cwill713/Solar-Panel-Phone-Charger/Simulations/Pictures of Output Voltage/0.05s.PNG

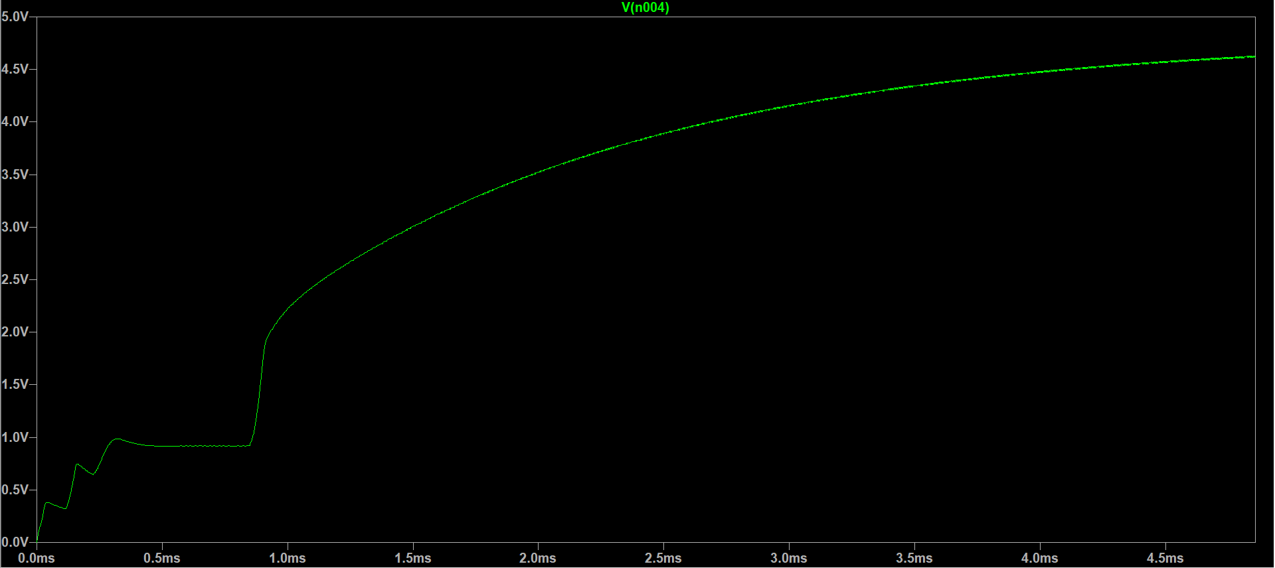
Simulations/Pictures of Output Voltage/0.05s.PNG
