cwill713/Solar-Panel-Phone-Charger/Simulations/Pictures of Output Voltage/Capture.PNG

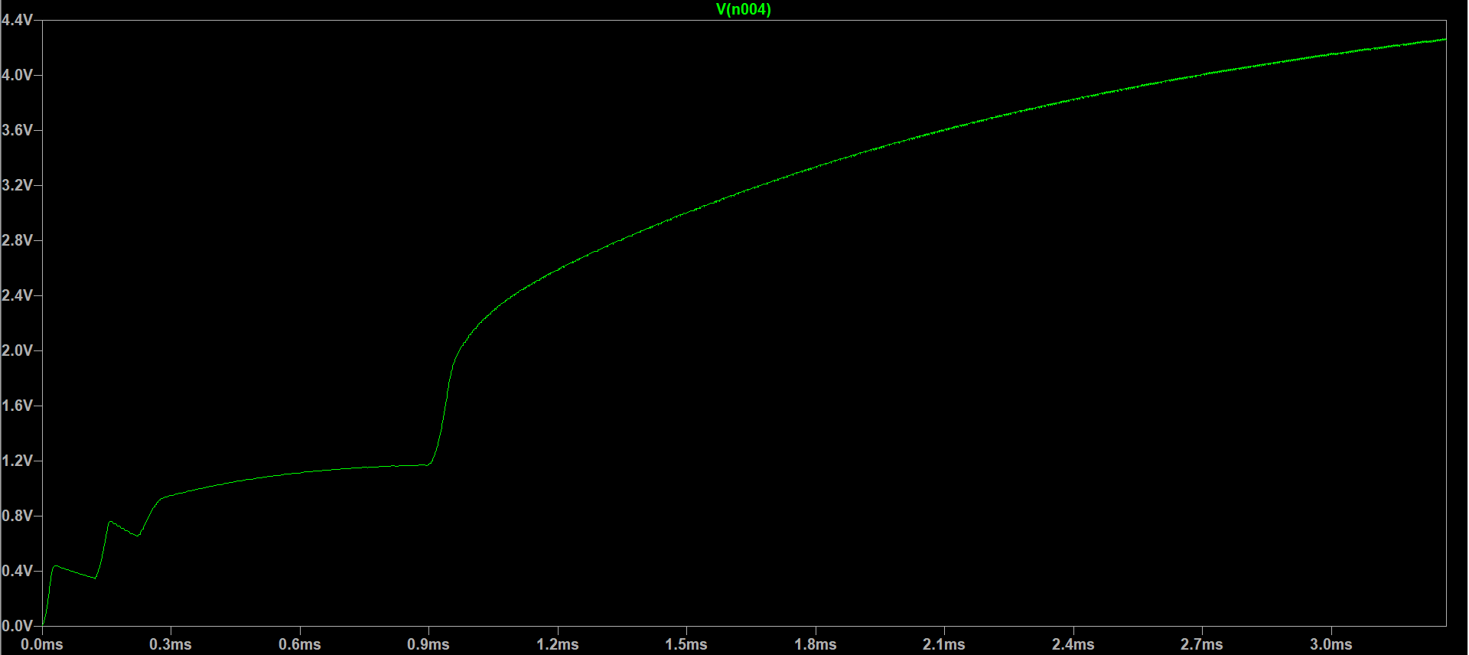
Simulations/Pictures of Output Voltage/Capture.PNG
