cwill713/Solar-Panel-Phone-Charger/Simulations/Pictures of Output Voltage/ThreeOutputVoltages.PNG

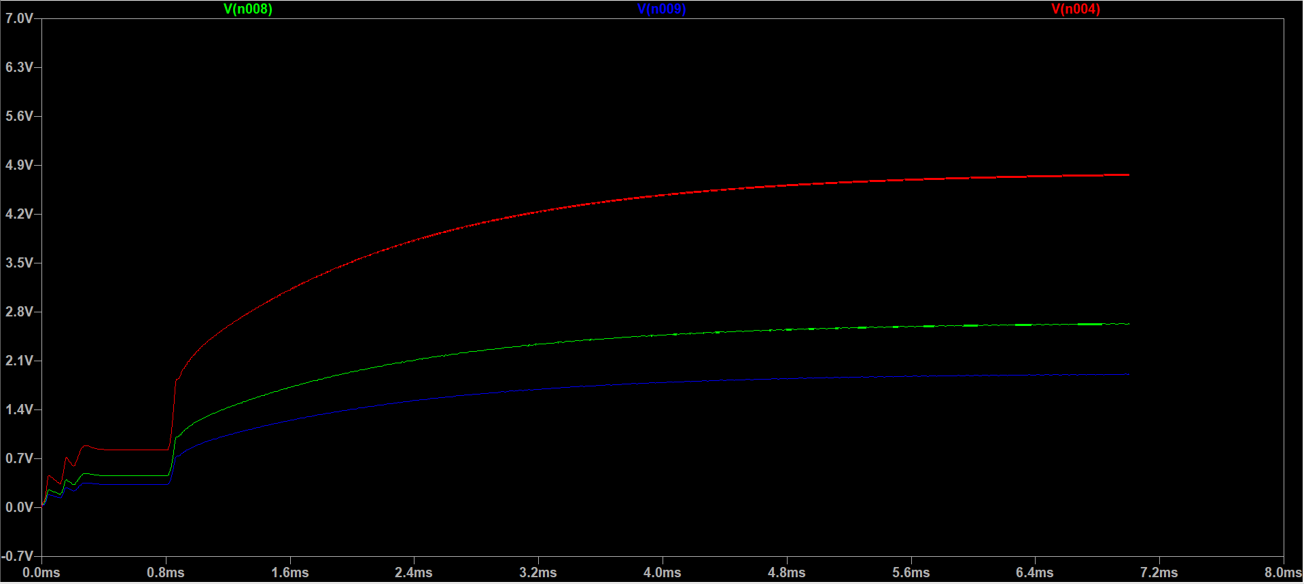
Simulations/Pictures of Output Voltage/ThreeOutputVoltages.PNG
