cwill713/Solar-Panel-Phone-Charger/Schematics/SolarChargerV3/PDF Files/SolarChargerV2-B_Silkscreen.pdf

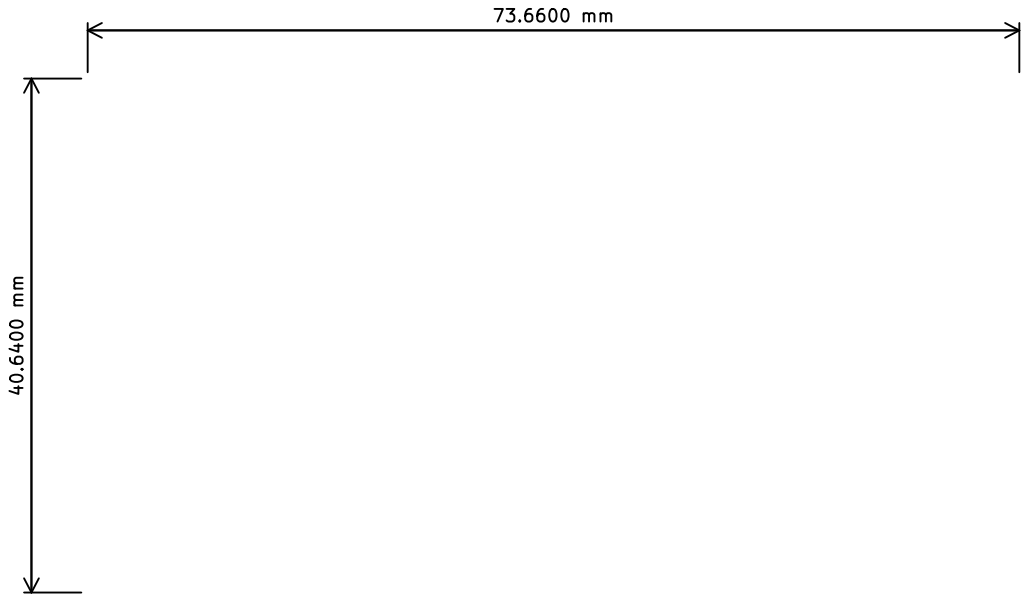
[picture p18: page 1]
