cwill713/Solar-Panel-Phone-Charger/Schematics/SolarChargerV3/PDF Files/SolarChargerV2-F_Cu.pdf

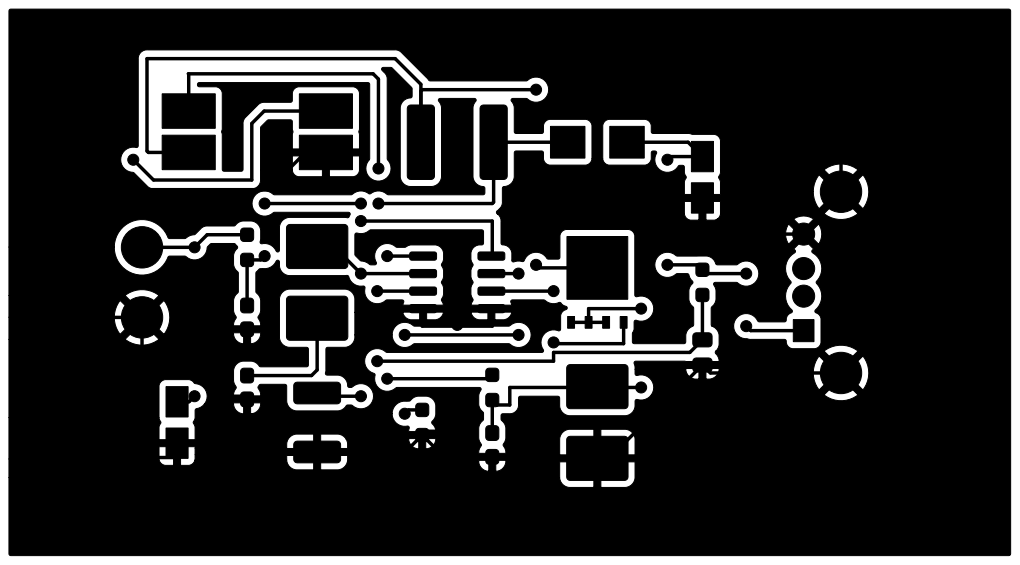
[picture p19: page 1]
