cwill713/Solar-Panel-Phone-Charger/Schematics/SolarChargerV3/PDF Files/SolarChargerV2-F_Fab.pdf

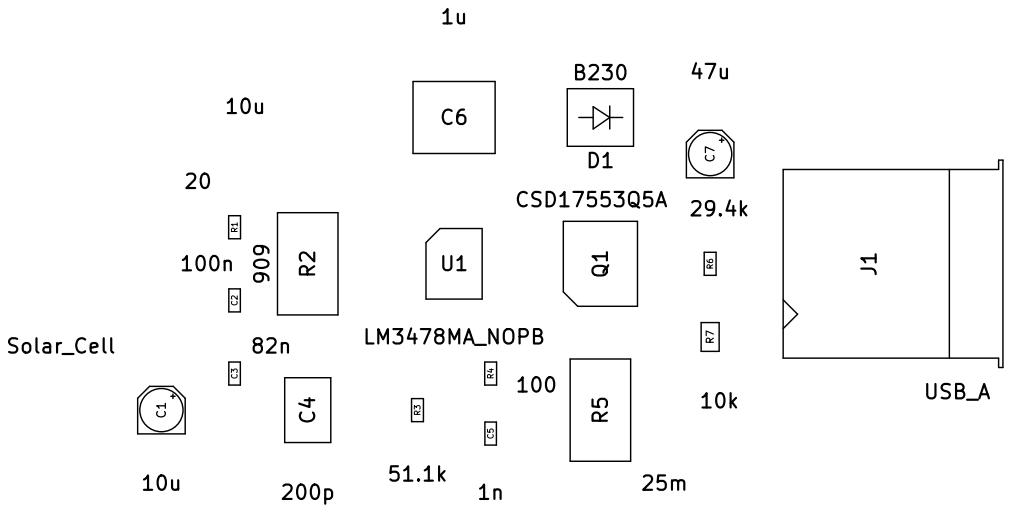
[picture p20: page 1]
