cwill713/Solar-Panel-Phone-Charger/Schematics/SolarChargerV3/PDF Files/SolarChargerV2-F_Mask.pdf

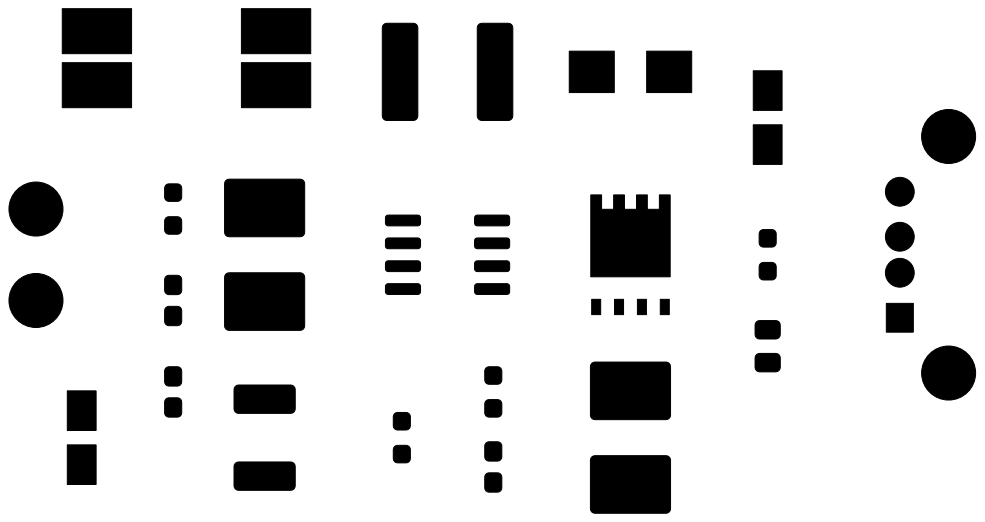
[picture p21: page 1]
