cwill713/Solar-Panel-Phone-Charger/Schematics/SolarChargerV3/PDF Files/SolarChargerV2-F_Silkscreen.pdf

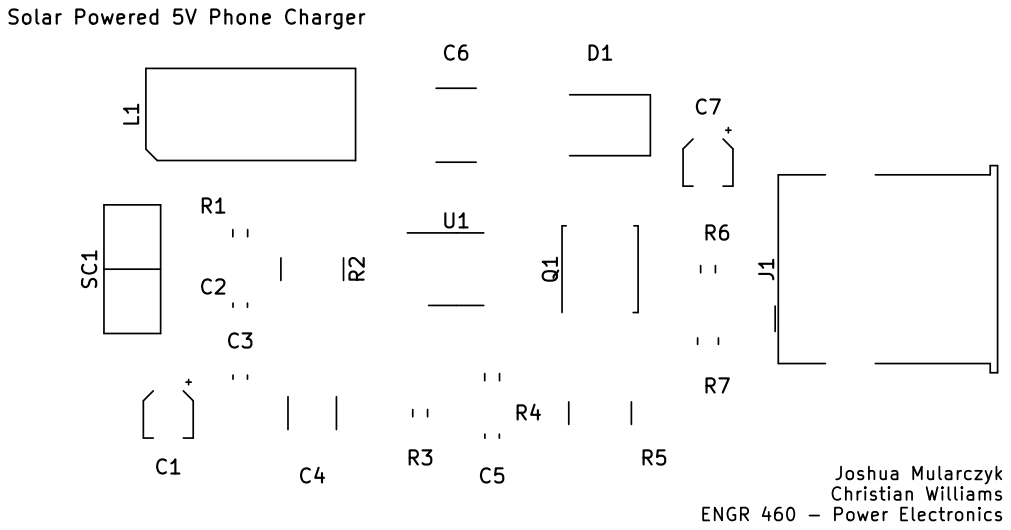
[picture p22: page 1]
