cwill713/Solar-Panel-Phone-Charger/Schematics/SolarChargerV4/PDF Files/SolarChargerV2-F_Cu.pdf

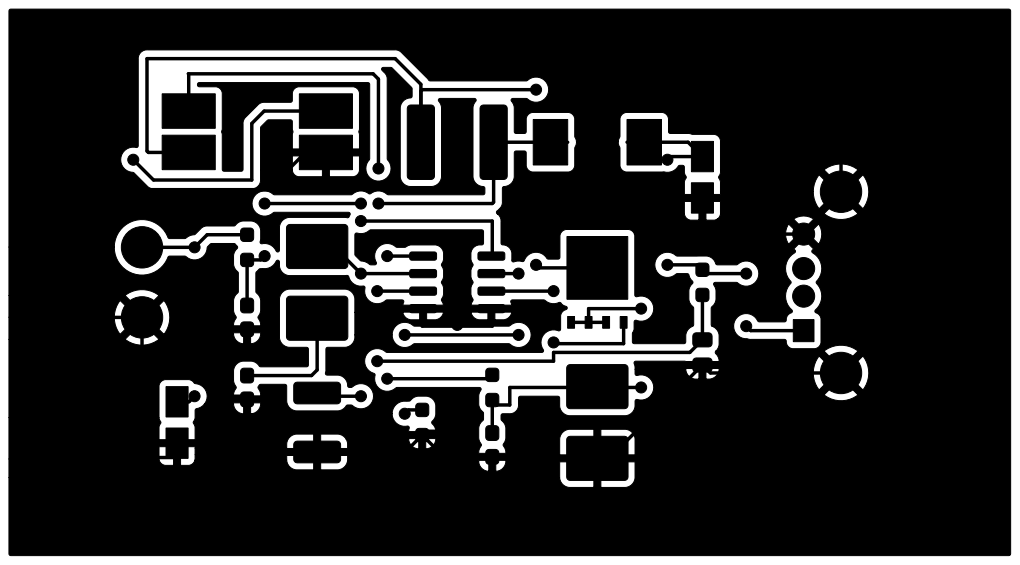
[picture p23: page 1]
