cwill713/Solar-Panel-Phone-Charger/Schematics/SolarChargerV4/PDF Files/SolarChargerV2-F_Fab.pdf

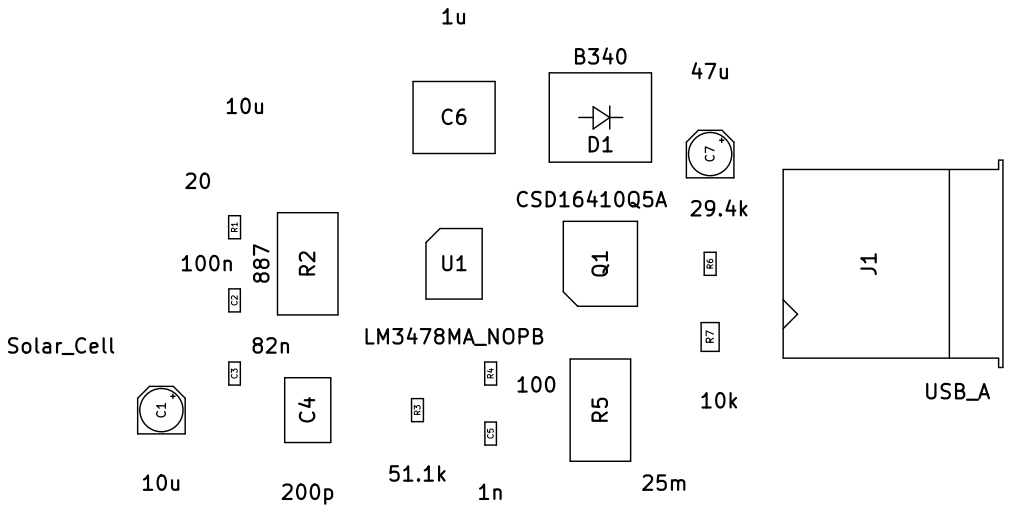
[picture p24: page 1]
