cwill713/Solar-Panel-Phone-Charger/Schematics/SolarChargerV4/PDF Files/SolarChargerV2-F_Mask.pdf

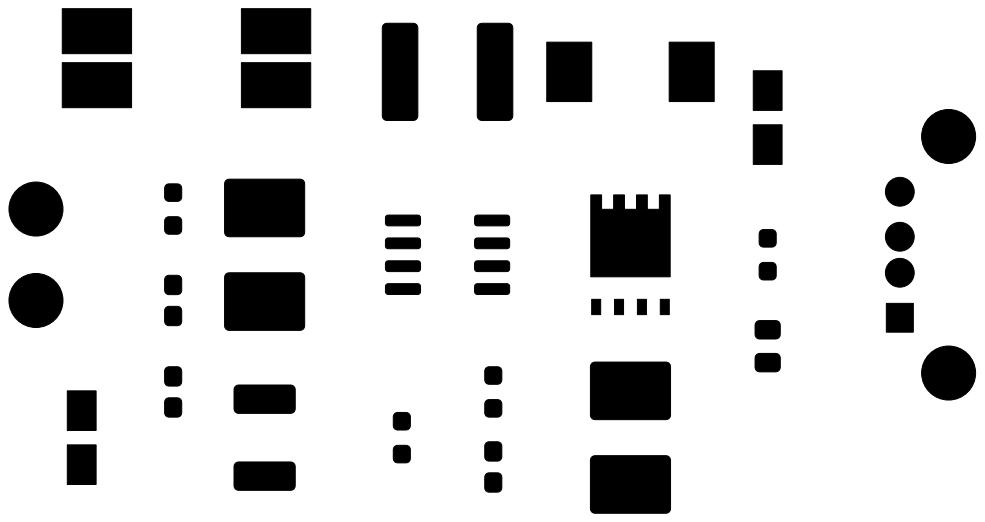
[picture p25: page 1]
