cwill713/Solar-Panel-Phone-Charger/Schematics/SolarChargerV4/PDF Files/SolarChargerV2-F_Silkscreen.pdf

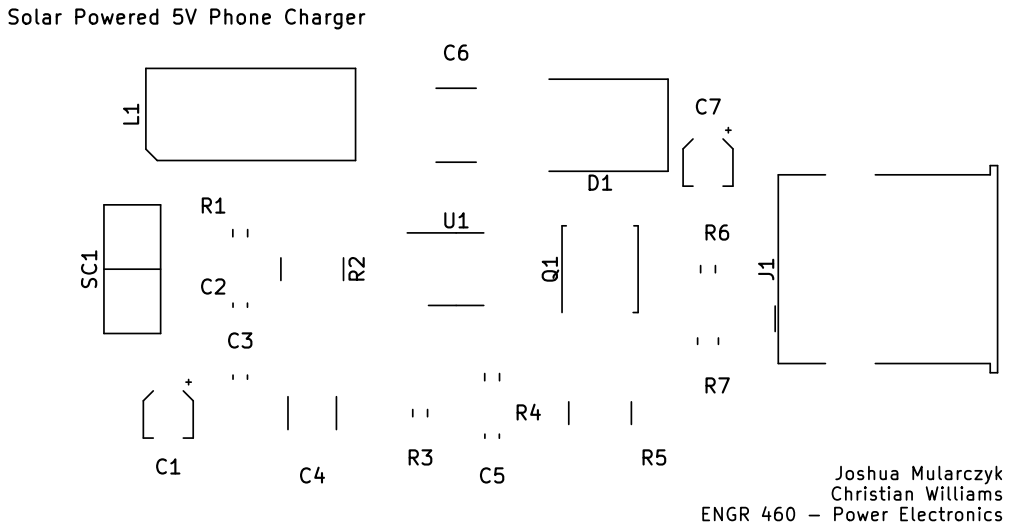
[picture p26: page 1]
