cwill713/Solar-Panel-Phone-Charger/Schematics/SolarChargerV5/PDFV5Files/SolarChargerV2-B_Cu.pdf

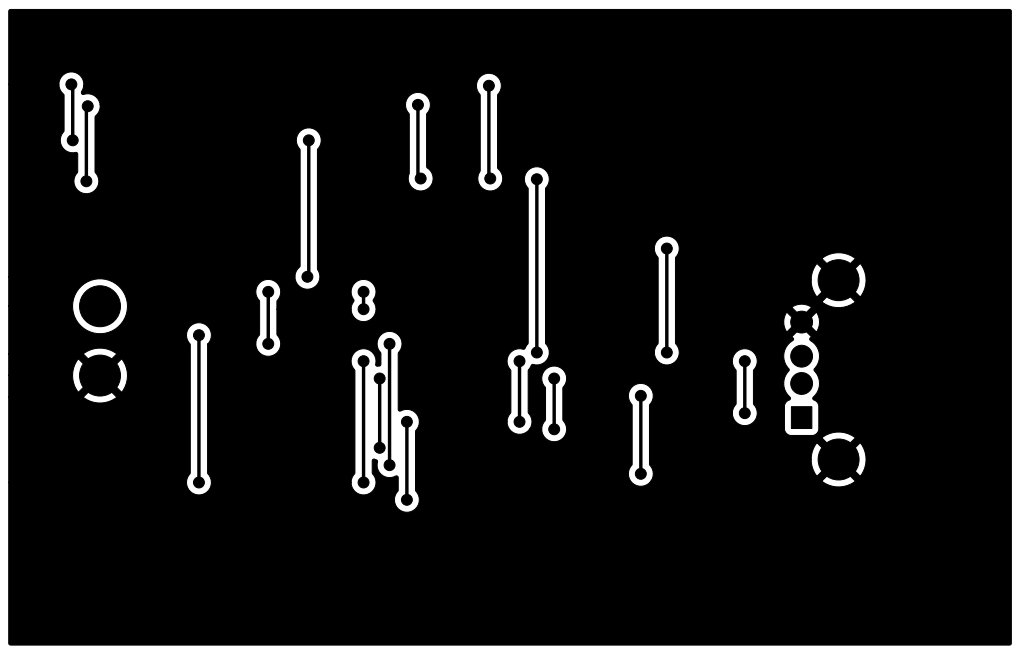
[picture p27: page 1]
