cwill713/Solar-Panel-Phone-Charger/Schematics/SolarChargerV5/PDFV5Files/SolarChargerV2-B_Mask.pdf

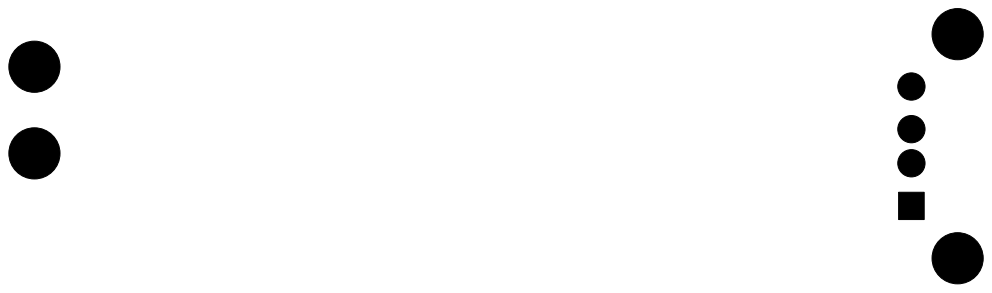
[picture p28: page 1]
