cwill713/Solar-Panel-Phone-Charger/Schematics/SolarChargerV5/PDFV5Files/SolarChargerV2-F_Cu.pdf

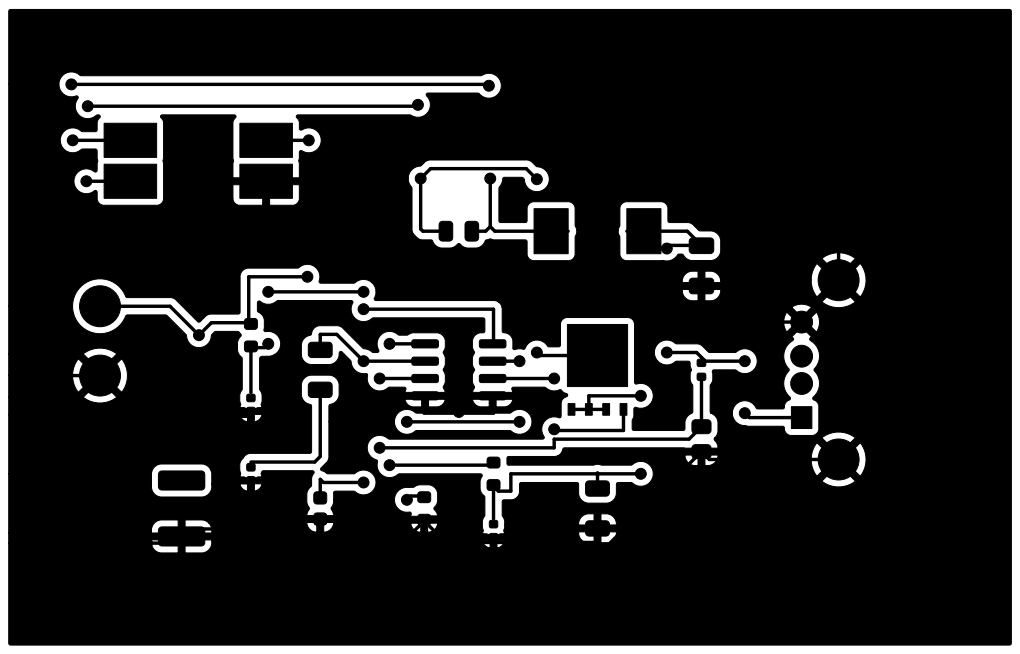
[picture p29: page 1]
