cwill713/Solar-Panel-Phone-Charger/Schematics/SolarChargerV5/PDFV5Files/SolarChargerV2-F_Fab.pdf

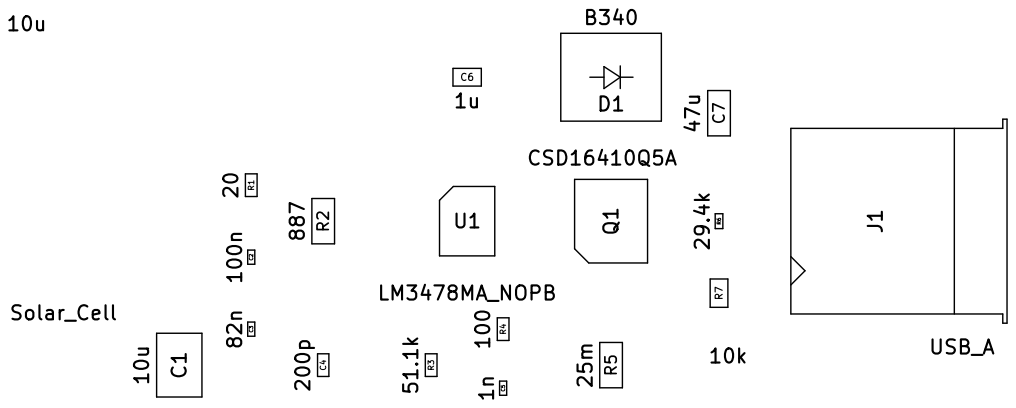
[picture p30: page 1]
