cwill713/Solar-Panel-Phone-Charger/Schematics/SolarChargerV5/PDFV5Files/SolarChargerV2-F_Mask.pdf

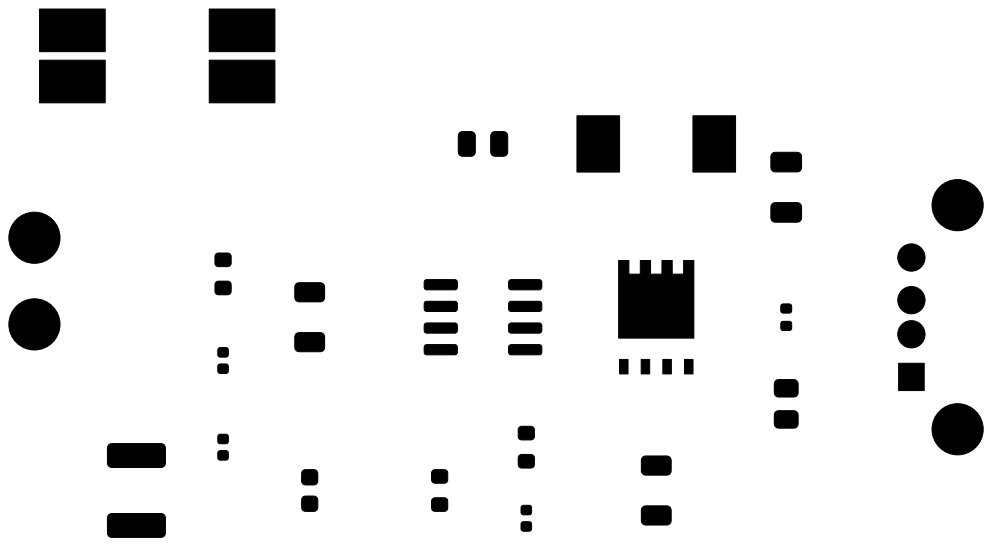
[picture p31: page 1]
