cwill713/Solar-Panel-Phone-Charger/Schematics/SolarChargerV5/PDFV5Files/SolarChargerV2-F_Silkscreen.pdf

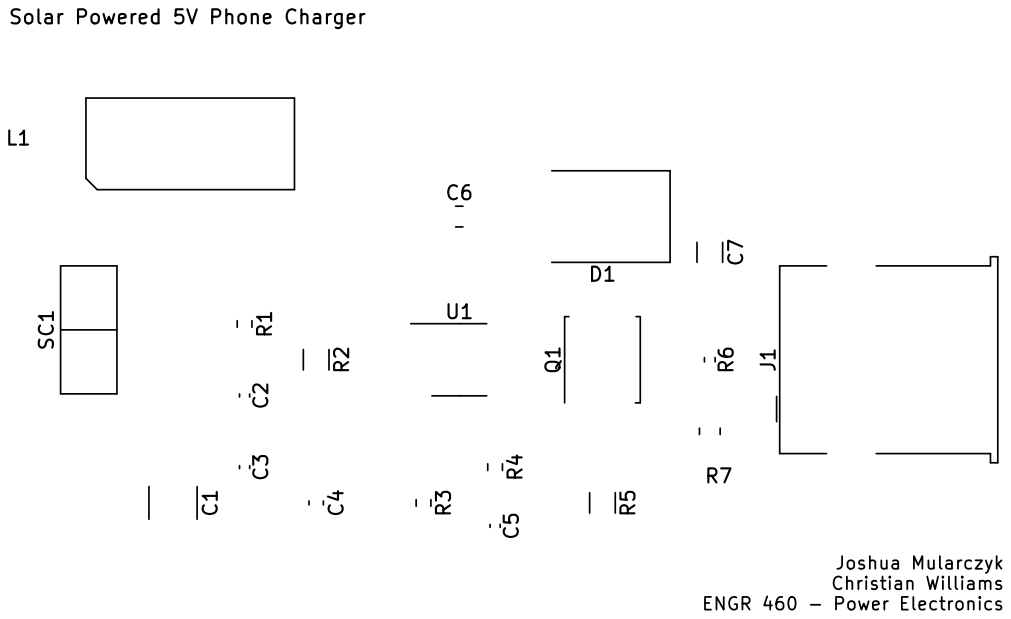
[picture p32: page 1]
