cwill713/Solar-Panel-Phone-Charger/Schematics/SolarChargerV6/PDFV6Files/SolarChargerV6-B_Cu.pdf

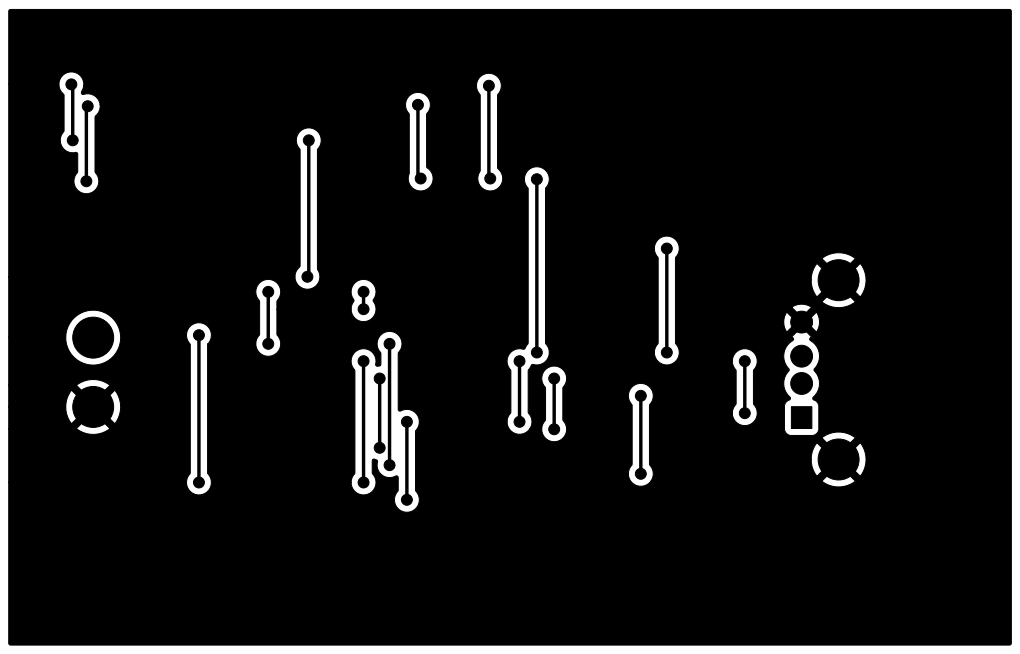
[picture p33: page 1]
