cwill713/Solar-Panel-Phone-Charger/Schematics/SolarChargerV6/PDFV6Files/SolarChargerV6-F_Cu.pdf

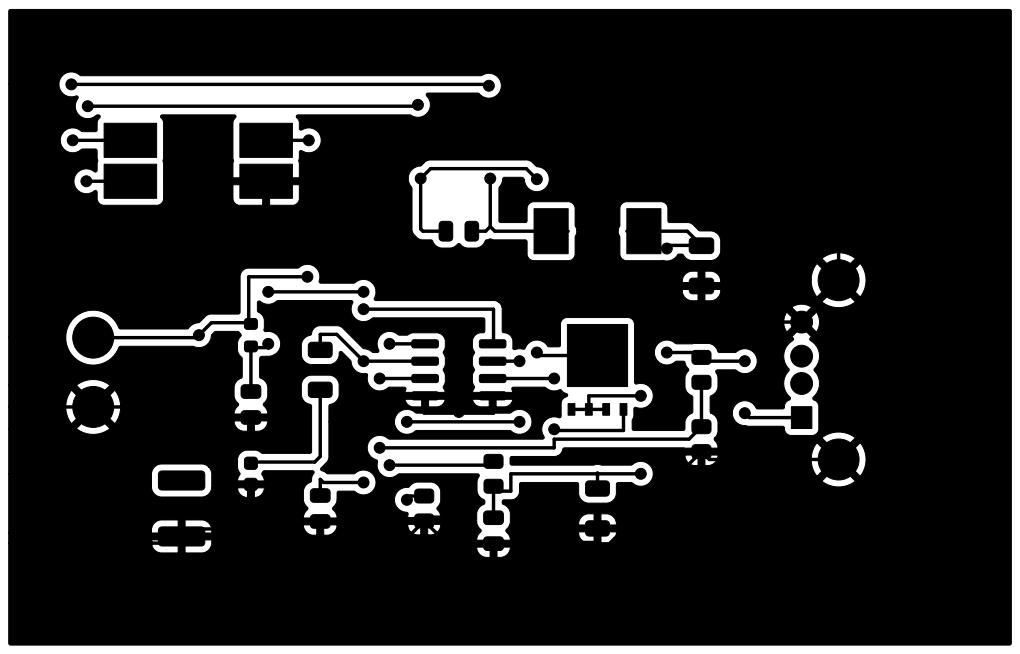
[picture p34: page 1]
