cwill713/Solar-Panel-Phone-Charger/Schematics/SolarChargerV6/PDFV6Files/SolarChargerV6-F_Fab.pdf

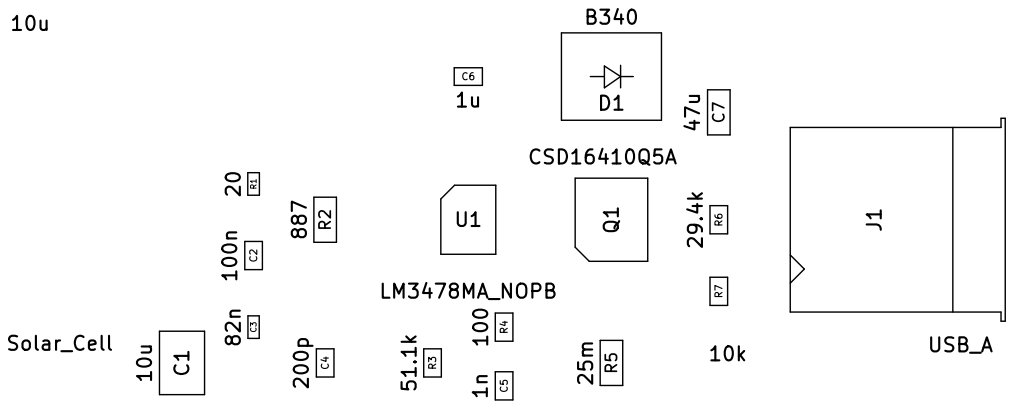
[picture p35: page 1]
