cwill713/Solar-Panel-Phone-Charger/Schematics/SolarChargerV6/PDFV6Files/SolarChargerV6-F_Mask.pdf

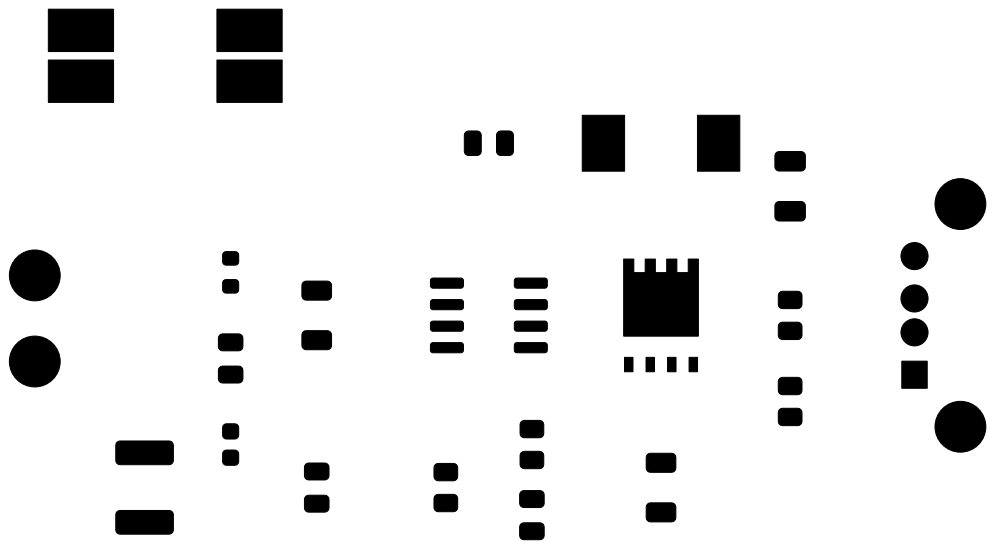
[picture p36: page 1]
