cwill713/Solar-Panel-Phone-Charger/Schematics/SolarChargerV6/PDFV6Files/SolarChargerV6-F_Silkscreen.pdf

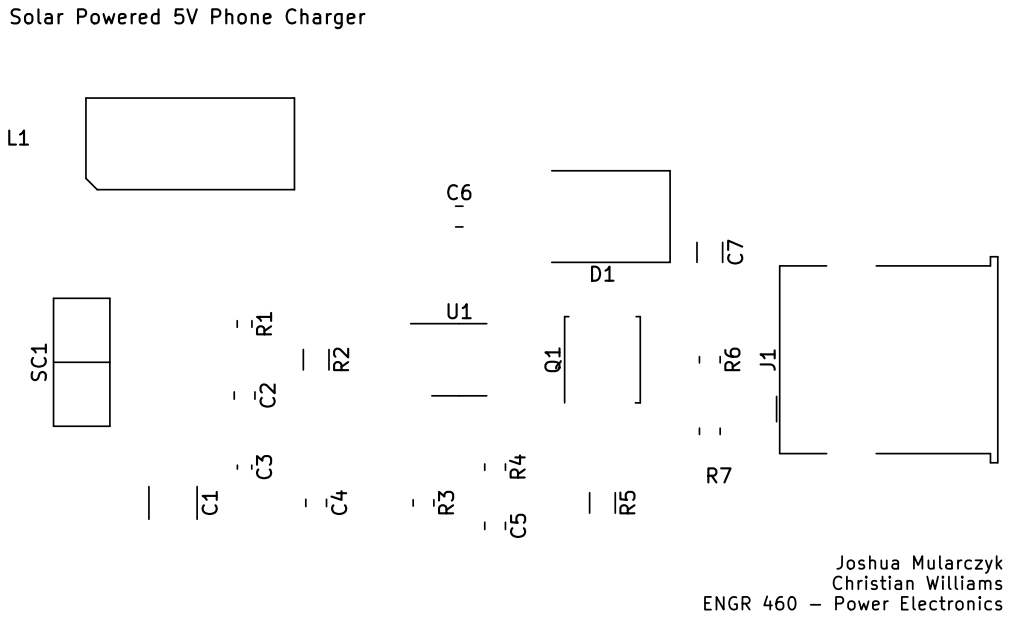
[picture p37: page 1]
