cwill713/Solar-Panel-Phone-Charger/Voltage Regulator Simulation.asc

C1: cap; 2200µ
C2: cap; 47µ
D1: diode
D2: diode
D3: diode
R1: res; 900
R2: res; 300
R3: res; 5
U1: LT317A
V1: voltage; 12V
Named nets: 0, Vout
.tran 15
